FrancisNGG/sms-forwarder/script/util_led.lua

local util_led = {}

--状态灯
local ledStatus= gpio.setup(12, 0, gpio.PULLUP)
--闪闪就行了
sys.taskInit(function()
    while true do
        ledStatus(1)
        sys.wait(100)
        ledStatus(0)
        sys.wait(1000)
    end
end)

--当前状态
--1：5秒一闪，模组未响应
--2：一直亮，没卡
--3：1秒一闪，没联网
--4：0.2秒一闪，正常运行
util_led.status = 1
local st = {5000,1,1000,200}
--事件灯
local ledDoing= gpio.setup(8, 0, gpio.PULLUP)
--闪闪就行了
sys.taskInit(function()
    while true do
        ledDoing(1)
        sys.wait(100)
        ledDoing(0)
        sys.wait(st[util_led.status])
    end
end)

return util_led
